Goomehh/SIV/Fotos/Funcionamiento del circuito sin la moto.jpg

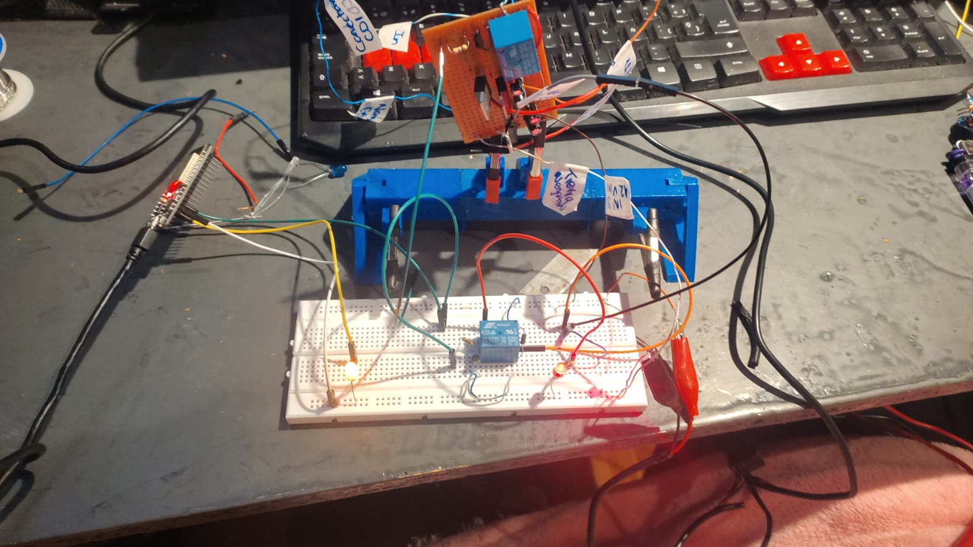
Fotos/Funcionamiento del circuito sin la moto.jpg
