Goomehh/SIV/Fotos/Modulo SIM800L.jpg

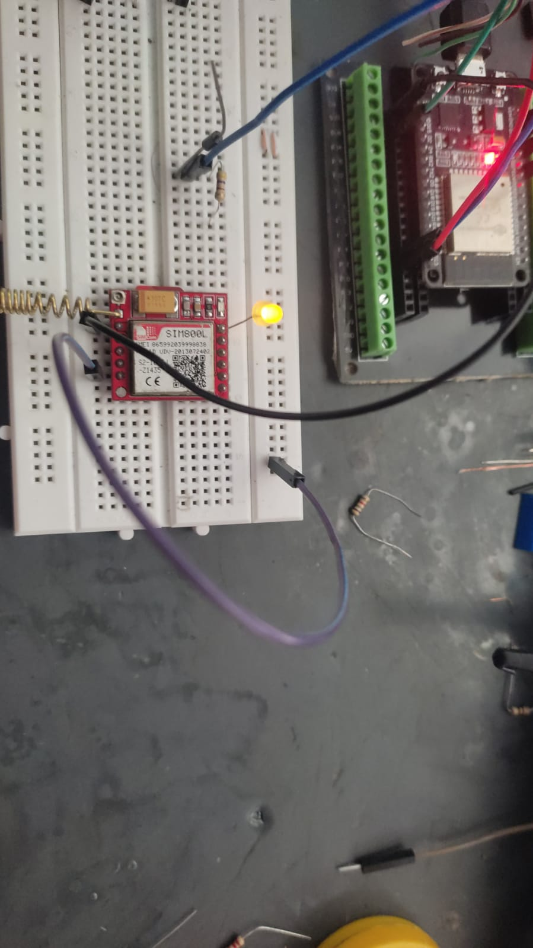
Fotos/Modulo SIM800L.jpg
