Goomehh/SIV/Fotos/Terminales del sensor de huella.jpg

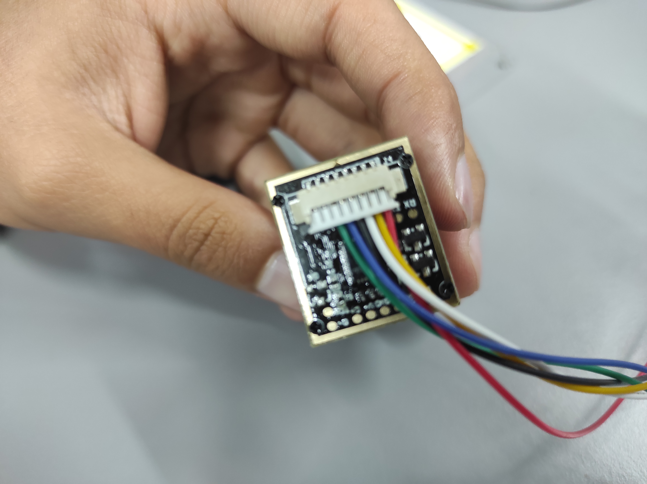
Fotos/Terminales del sensor de huella.jpg
