Goomehh/SIV/Fotos/WhatsApp Image 2023-06-26 at 7.27.10 AM (2).jpeg

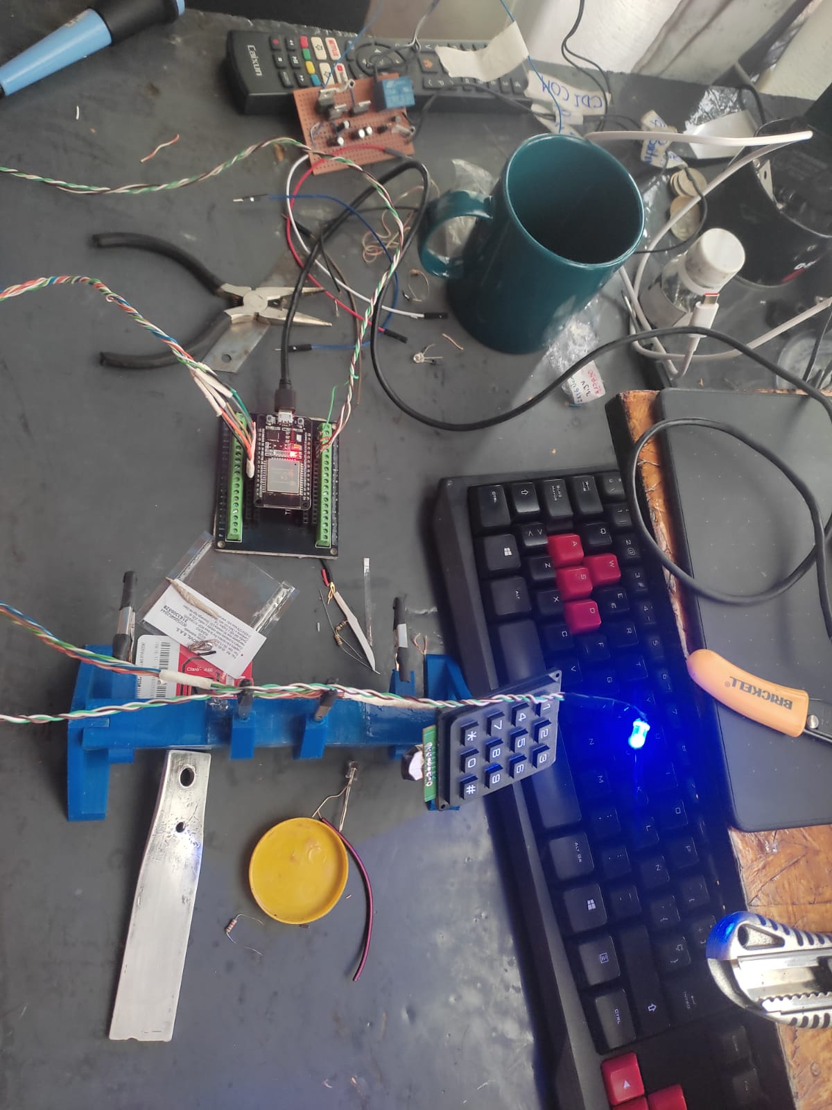
Fotos/WhatsApp Image 2023-06-26 at 7.27.10 AM (2).jpeg
