Goomehh/SIV/Fotos/WhatsApp Image 2023-06-26 at 7.27.11 AM (4).jpeg

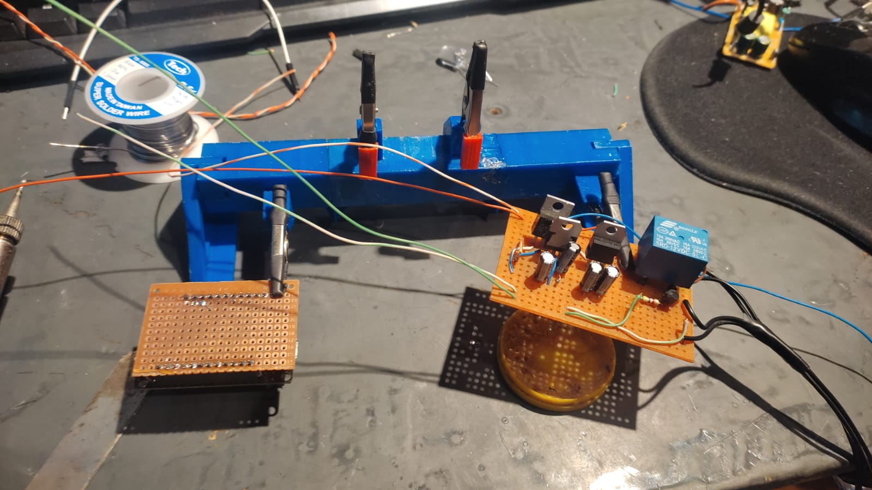
Fotos/WhatsApp Image 2023-06-26 at 7.27.11 AM (4).jpeg
