Goomehh/SIV/Fotos/WhatsApp Image 2023-06-26 at 7.27.12 AM (2).jpeg

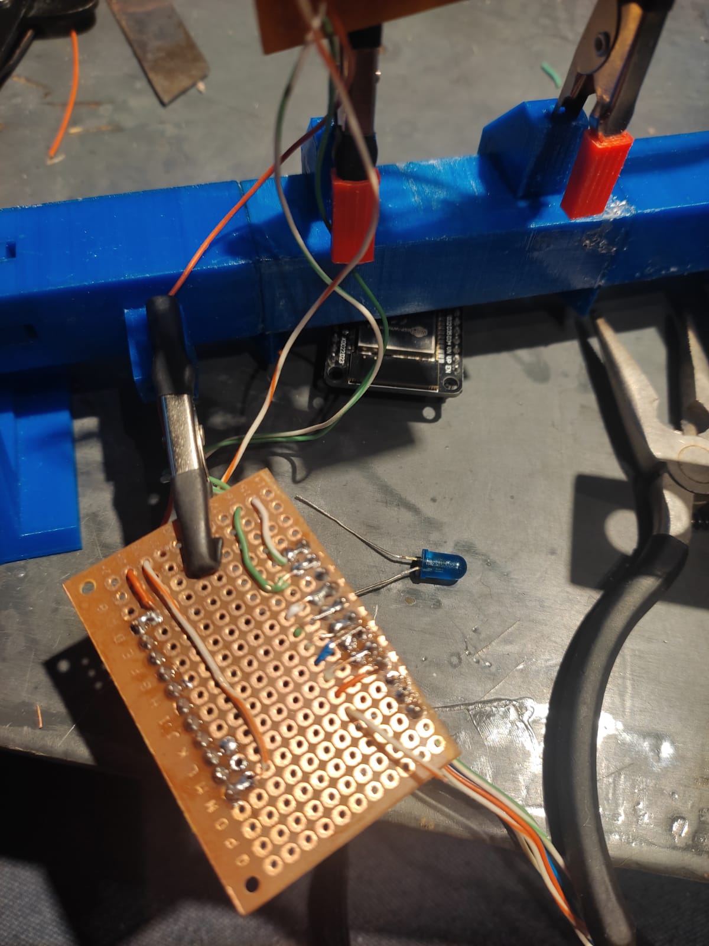
Fotos/WhatsApp Image 2023-06-26 at 7.27.12 AM (2).jpeg
